elcano/Linked/LinkedVehicles-Winter-Spring2023/CAD/Trike assembly/cylinder.SLDPRT

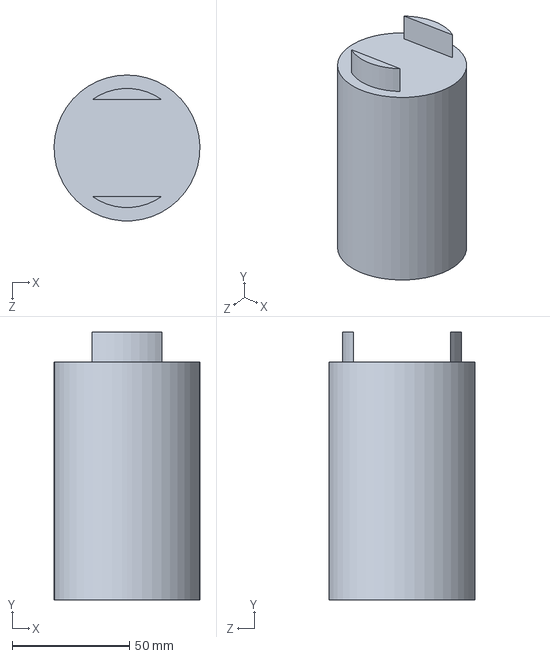
[picture p67: CAD file, 2023-06-08]
LinkedVehicles-Winter-Spring2023/CAD/Trike assembly/cylinder.SLDPRT
62.2 x 114.3 x 62.2 mm
