elcano/Linked/3_wire_connector_top.SLDPRT

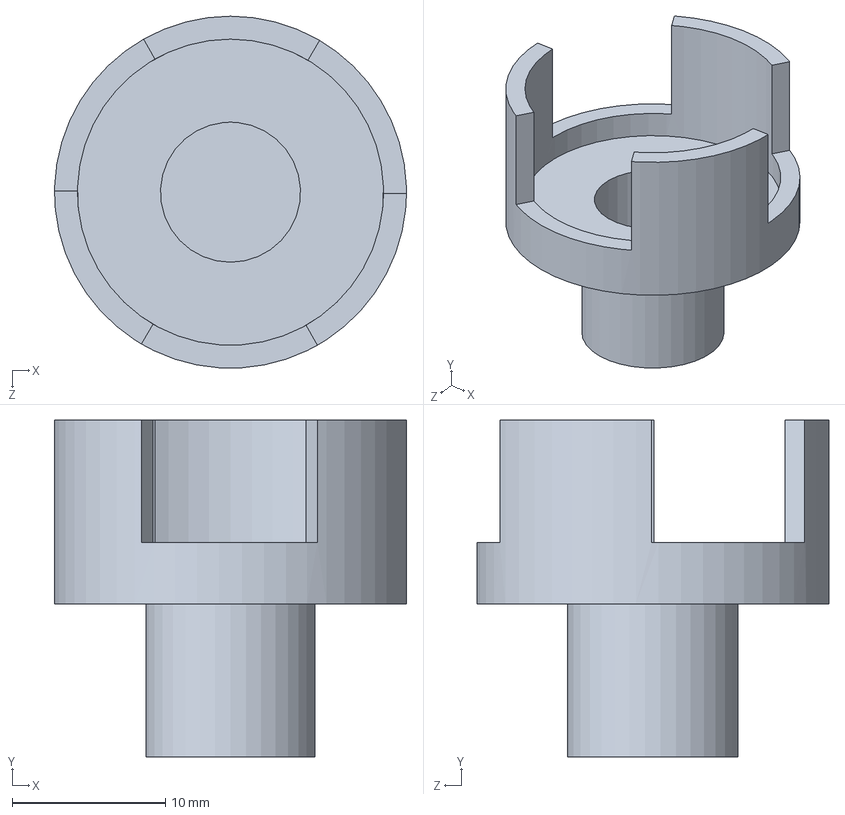
[picture p68: CAD file, 2023-06-08]
3_wire_connector_top.SLDPRT
23.0 x 22.0 x 23.0 mm
