elcano/Linked/LinkedVehicles-Winter-Spring2023/CAD/male and female- v2/UJoint.SLDPRT

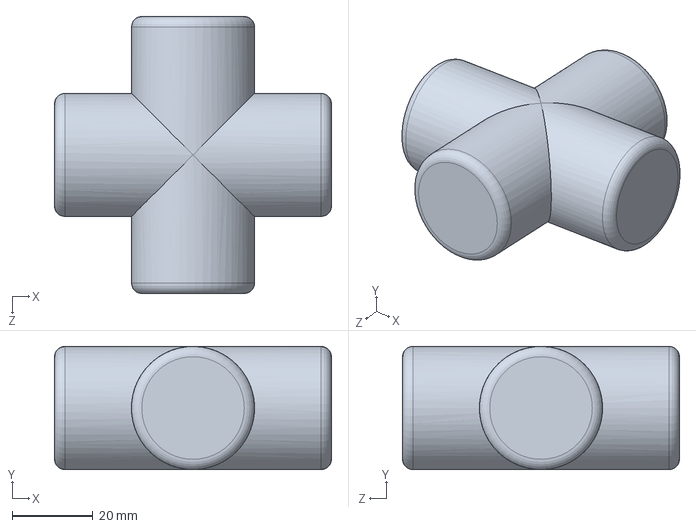
[picture p69: CAD file, 2023-06-08]
LinkedVehicles-Winter-Spring2023/CAD/male and female- v2/UJoint.SLDPRT
68.6 x 30.5 x 68.6 mm
