elcano/Linked/LinkedVehicles-Winter-Spring2023/CAD/male and female/Yoke2.SLDPRT

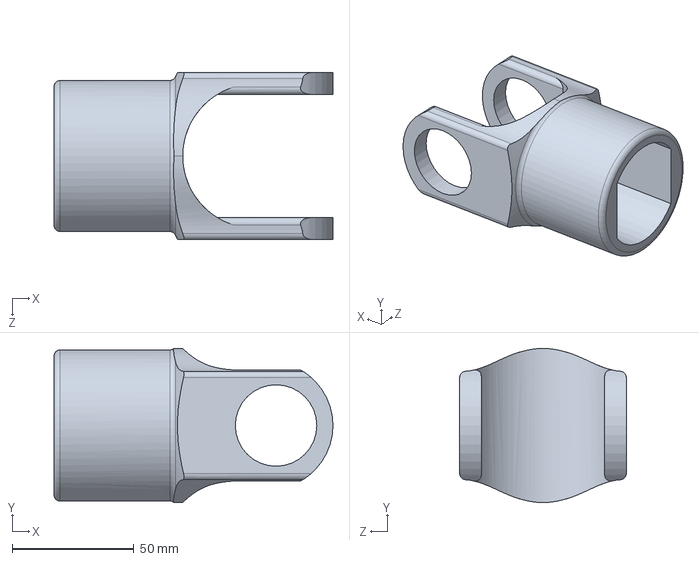
[picture p70: CAD file, 2023-06-08]
LinkedVehicles-Winter-Spring2023/CAD/male and female/Yoke2.SLDPRT
114.8 x 63.5 x 68.6 mm
