elcano/Linked/LinkedVehicles-Winter-Spring2023/CAD/Proto Lock 1.0/Rail_tapped hole.SLDPRT

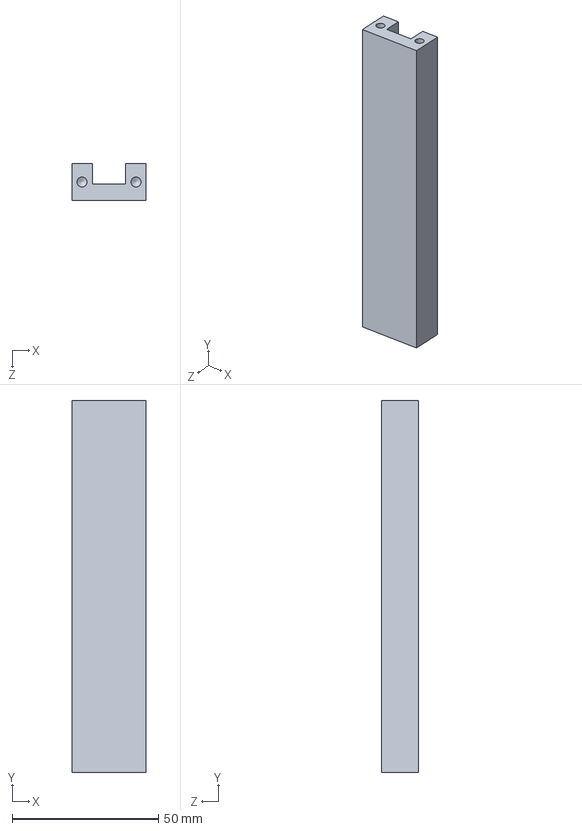
[picture p71: CAD file, 2023-06-08]
LinkedVehicles-Winter-Spring2023/CAD/Proto Lock 1.0/Rail_tapped hole.SLDPRT
25.4 x 127.0 x 12.7 mm
