elcano/Linked/LinkedVehicles-Winter-Spring2023/CAD/Proto Lock 2.0/Spool.SLDPRT

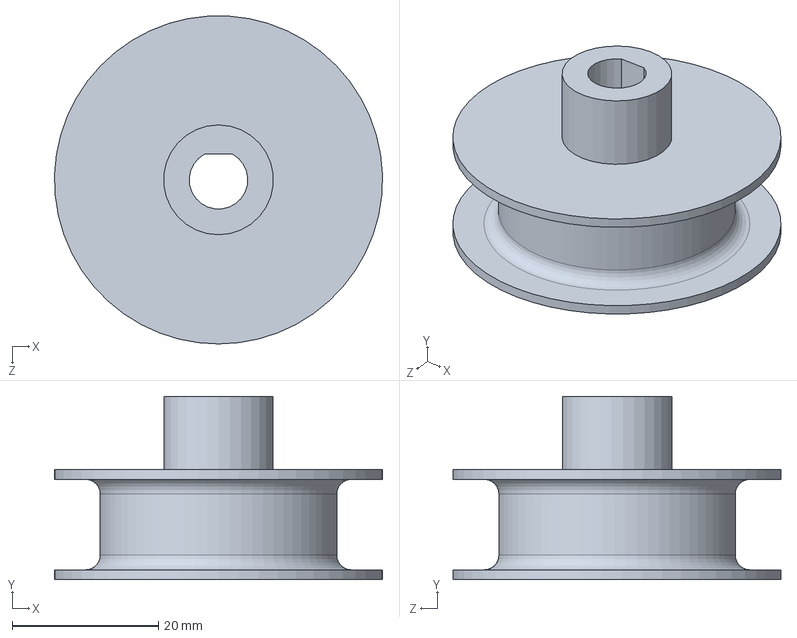
[picture p72: CAD file, 2023-06-08]
LinkedVehicles-Winter-Spring2023/CAD/Proto Lock 2.0/Spool.SLDPRT
44.8 x 25.0 x 44.8 mm
