elcano/Linked/LinkedVehicles-Winter-Spring2023/CAD/Trike assembly/Back mount plate.SLDPRT

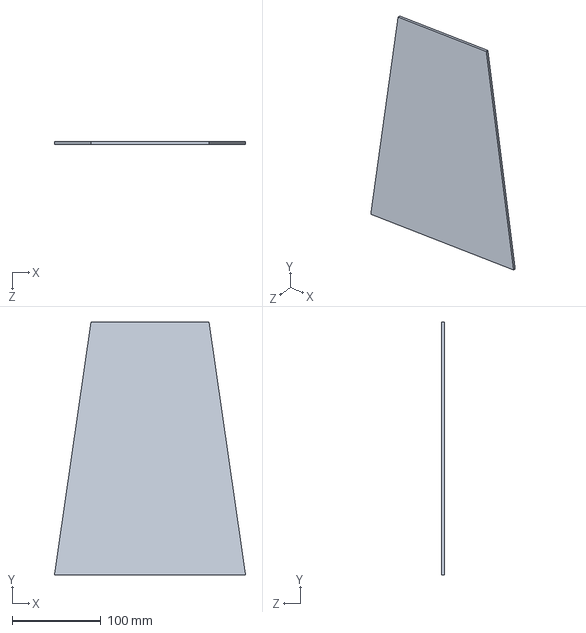
[picture p73: CAD file, 2023-06-08]
LinkedVehicles-Winter-Spring2023/CAD/Trike assembly/Back mount plate.SLDPRT
215.9 x 285.8 x 3.26 mm
