elcano/Linked/Cable_mangment_28mm.SLDPRT

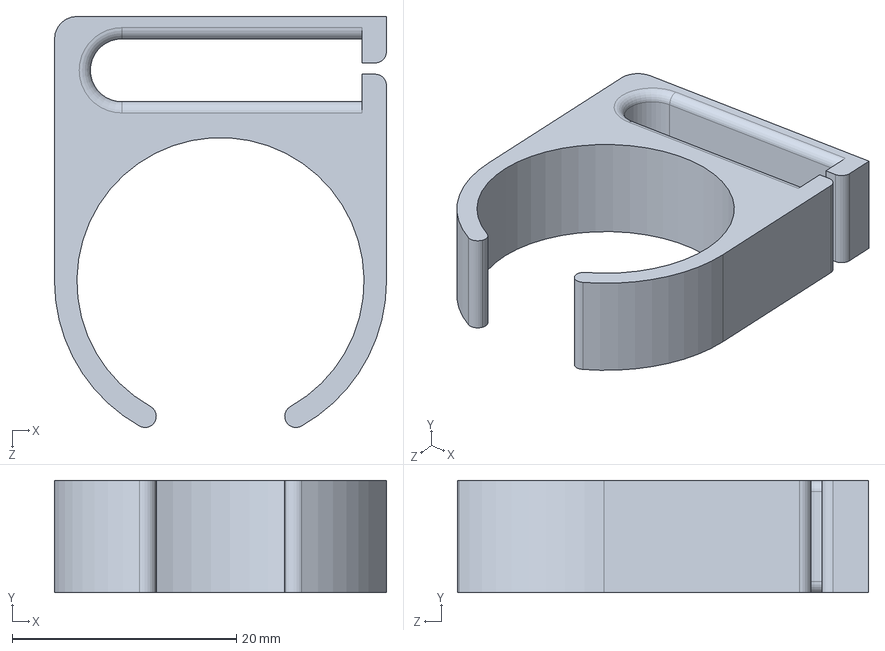
[picture p74: CAD file, 2023-06-08]
Cable_mangment_28mm.SLDPRT
29.6 x 10.0 x 36.7 mm
