elcano/Linked/LinkedVehicles-Winter-Spring2023/CAD/male and female- v2/lever lock.SLDPRT

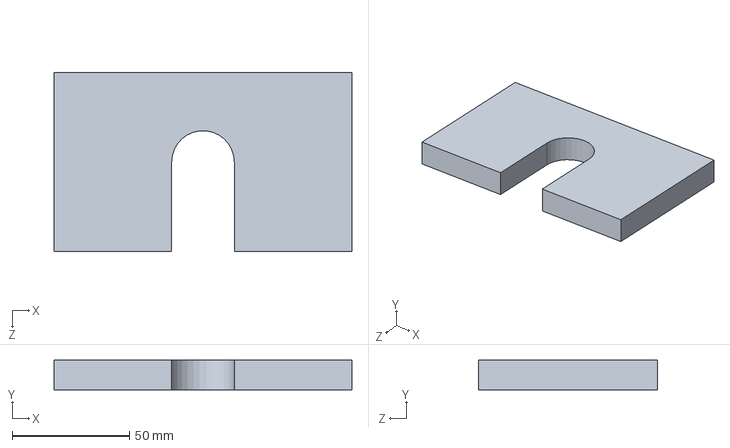
[picture p75: CAD file, 2023-06-08]
LinkedVehicles-Winter-Spring2023/CAD/male and female- v2/lever lock.SLDPRT
127.0 x 12.7 x 76.2 mm
