elcano/Linked/LinkedVehicles-Winter-Spring2023/CAD/New Female Part/Female Coupler Stock Materials.SLDPRT

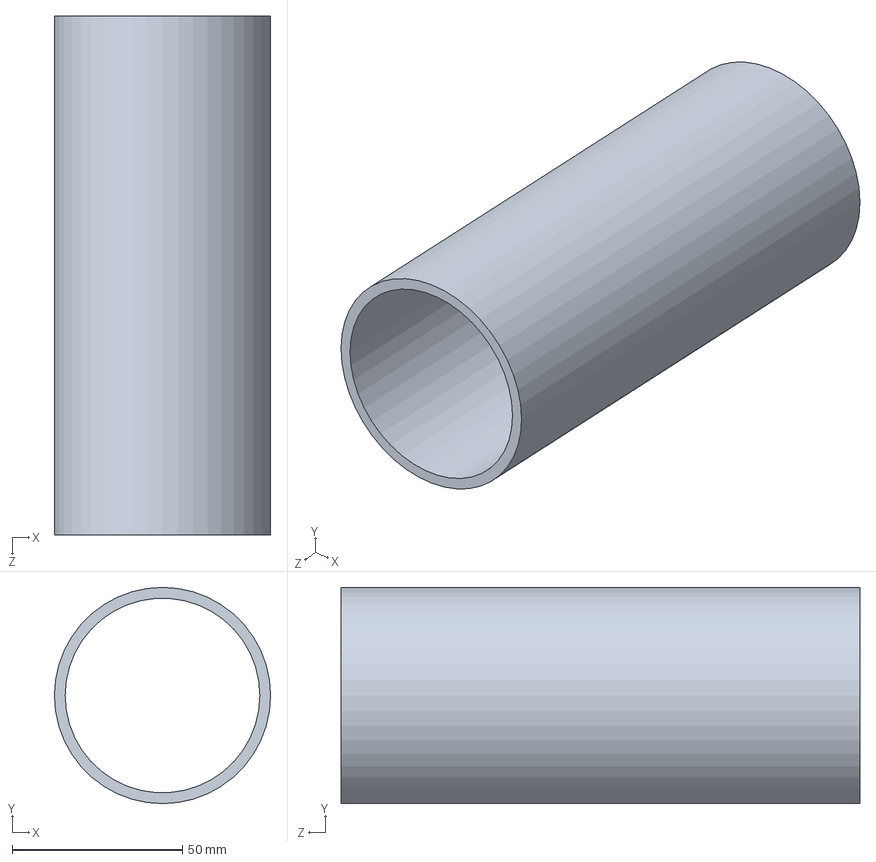
[picture p76: CAD file, 2023-06-08]
LinkedVehicles-Winter-Spring2023/CAD/New Female Part/Female Coupler Stock Materials.SLDPRT
63.5 x 63.5 x 152.4 mm
