elcano/Linked/LinkedVehicles-Winter-Spring2023/CAD/Proto Lock 2.0/Stepper.SLDPRT

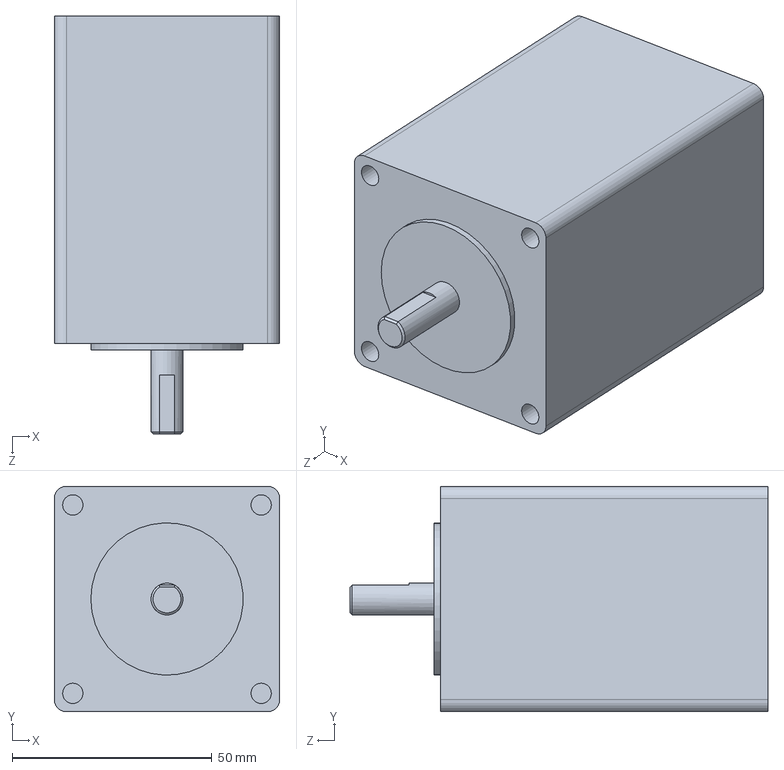
[picture p77: CAD file, 2023-06-08]
LinkedVehicles-Winter-Spring2023/CAD/Proto Lock 2.0/Stepper.SLDPRT
56.4 x 56.4 x 104.6 mm
