elcano/Linked/51_mm_tube_cable_mount.SLDPRT

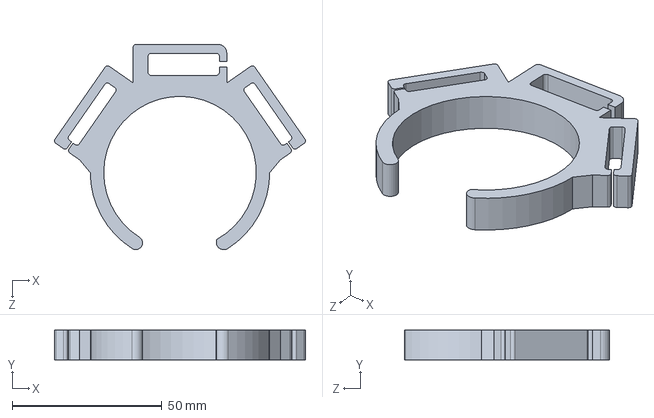
[picture p78: CAD file, 2023-06-08]
51_mm_tube_cable_mount.SLDPRT
83.9 x 10.0 x 68.7 mm
