elcano/Linked/LinkedVehicles-Winter-Spring2023/CAD/Trike assembly/Front mounting frame.SLDPRT

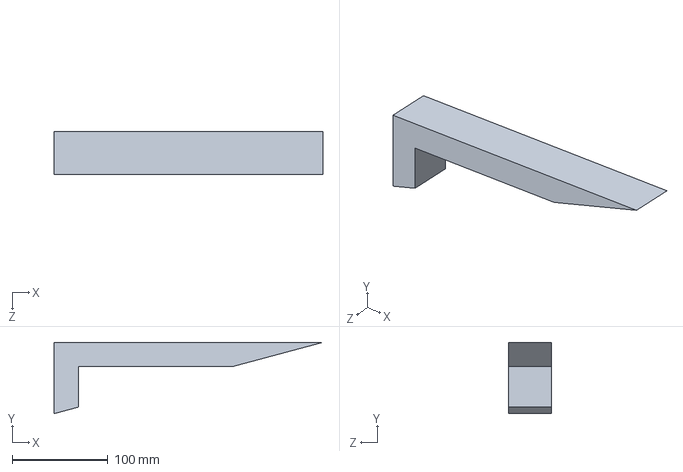
[picture p79: CAD file, 2023-06-08]
LinkedVehicles-Winter-Spring2023/CAD/Trike assembly/Front mounting frame.SLDPRT
280.4 x 74.3 x 45.0 mm
