elcano/Linked/LinkedVehicles-Winter-Spring2023/CAD/Proto Lock 1.0/CROSS.SLDPRT

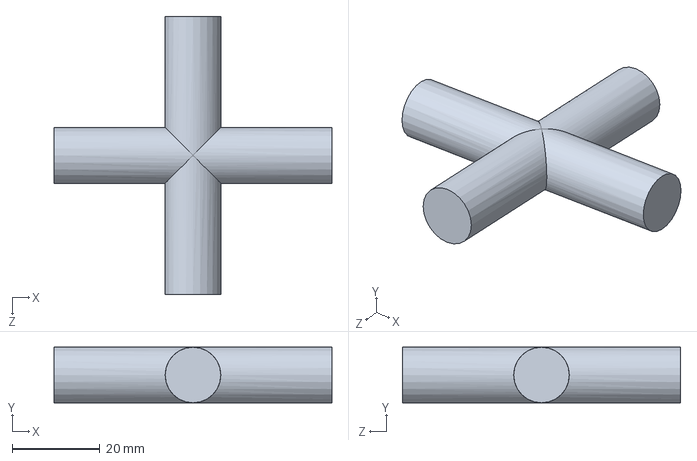
[picture p80: CAD file, 2023-06-08]
LinkedVehicles-Winter-Spring2023/CAD/Proto Lock 1.0/CROSS.SLDPRT
63.5 x 12.7 x 63.5 mm
