elcano/Linked/LinkedVehicles-Winter-Spring2023/CAD/Proto Lock 2.0/Pulley system pulley.SLDPRT

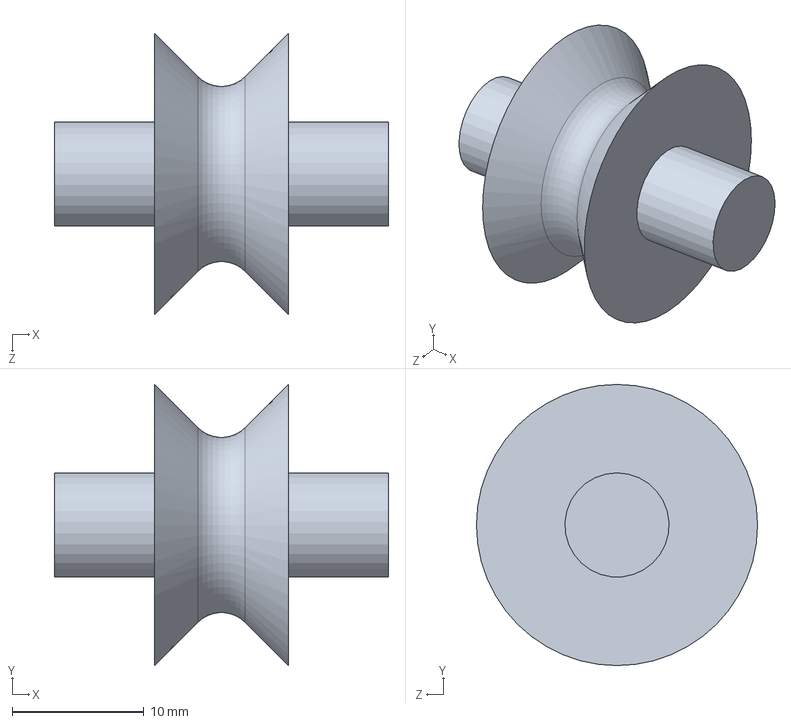
[picture p81: CAD file, 2023-06-08]
LinkedVehicles-Winter-Spring2023/CAD/Proto Lock 2.0/Pulley system pulley.SLDPRT
25.4 x 21.4 x 21.4 mm
