elcano/Linked/LinkedVehicles-Winter-Spring2023/CAD/Proto Lock 1.0/Lever lock.SLDPRT

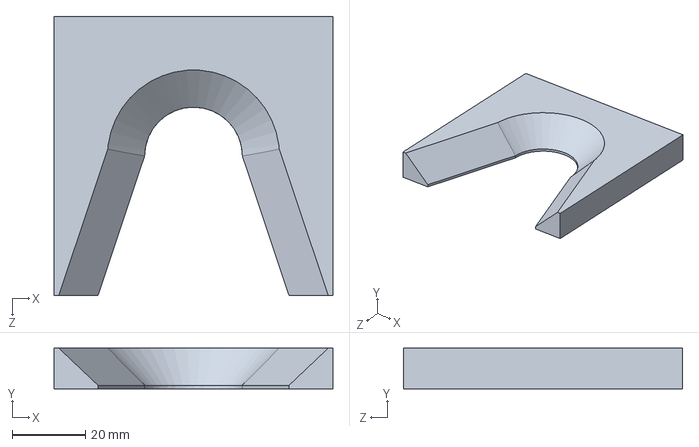
[picture p82: CAD file, 2023-06-08]
LinkedVehicles-Winter-Spring2023/CAD/Proto Lock 1.0/Lever lock.SLDPRT
76.2 x 11.1 x 76.2 mm
