elcano/Linked/LinkedVehicles-Winter-Spring2023/CAD/Proto Lock 2.0/Temp Bumper.SLDPRT

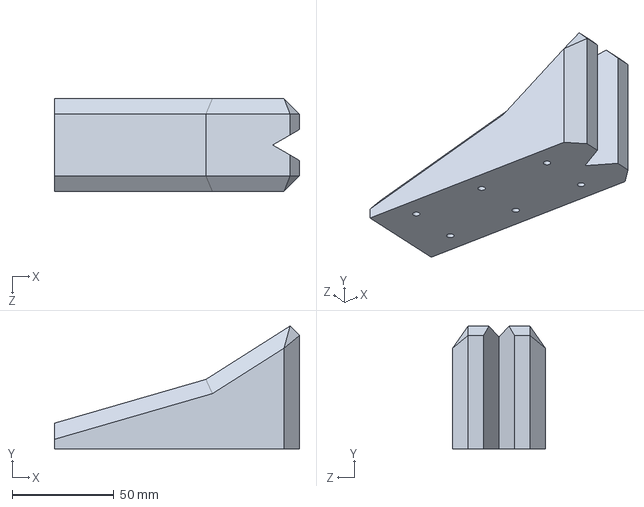
[picture p83: CAD file, 2023-06-08]
LinkedVehicles-Winter-Spring2023/CAD/Proto Lock 2.0/Temp Bumper.SLDPRT
120.7 x 60.5 x 45.7 mm
