elcano/Linked/LinkedVehicles-Winter-Spring2023/CAD/Trike assembly/Male Shaft (2).SLDPRT

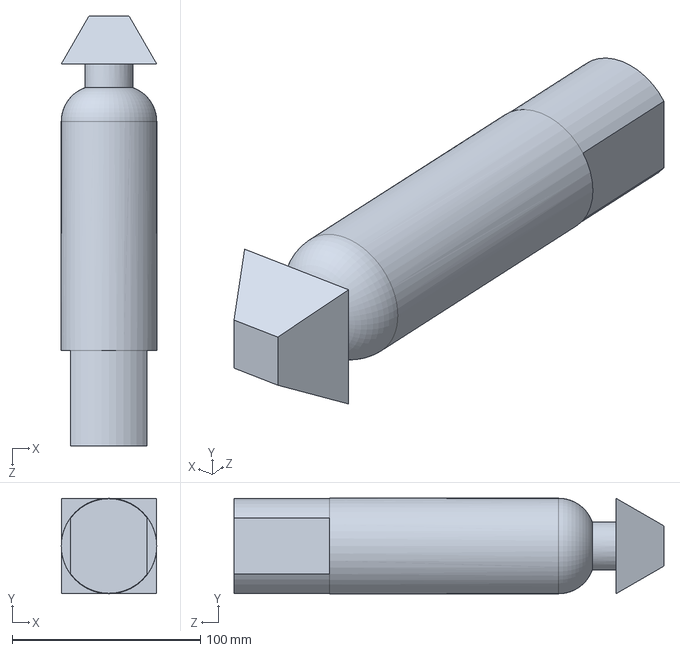
[picture p84: CAD file, 2023-06-08]
LinkedVehicles-Winter-Spring2023/CAD/Trike assembly/Male Shaft (2).SLDPRT
50.8 x 50.8 x 228.6 mm
