elcano/Linked/LinkedVehicles-Winter-Spring2023/CAD/male and female/lever lock.SLDPRT

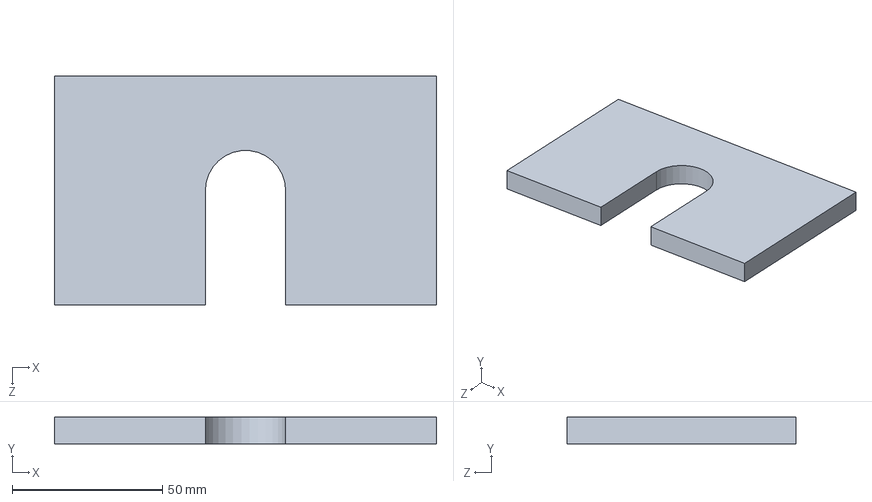
[picture p85: CAD file, 2023-06-08]
LinkedVehicles-Winter-Spring2023/CAD/male and female/lever lock.SLDPRT
127.0 x 8.89 x 76.2 mm
