elcano/Linked/LinkedVehicles-Winter-Spring2023/CAD/Proto Lock 1.0/1x.5 barstock.SLDPRT

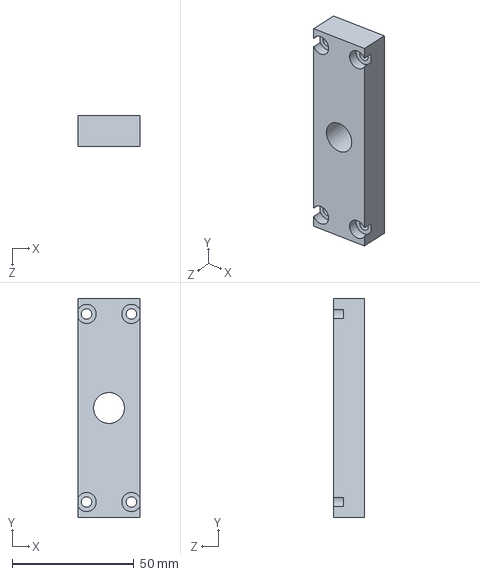
[picture p86: CAD file, 2023-06-08]
LinkedVehicles-Winter-Spring2023/CAD/Proto Lock 1.0/1x.5 barstock.SLDPRT
25.4 x 90.0 x 12.7 mm
