elcano/Linked/LinkedVehicles-Winter-Spring2023/CAD/Proto Lock 2.0/Baseplate V2.SLDPRT

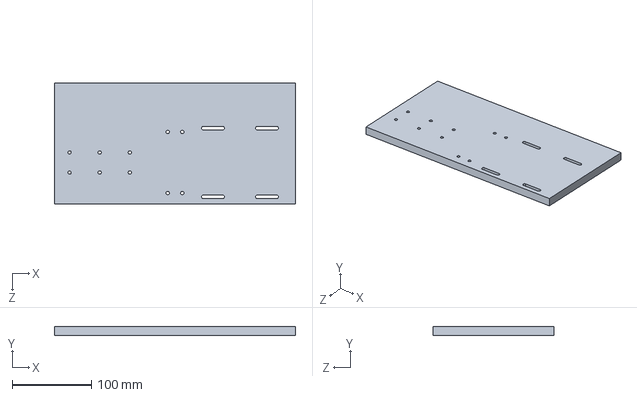
[picture p87: CAD file, 2023-06-08]
LinkedVehicles-Winter-Spring2023/CAD/Proto Lock 2.0/Baseplate V2.SLDPRT
304.8 x 11.1 x 152.4 mm
