elcano/Linked/LinkedVehicles-Winter-Spring2023/CAD/Proto Lock 1.0/ARMS.SLDPRT

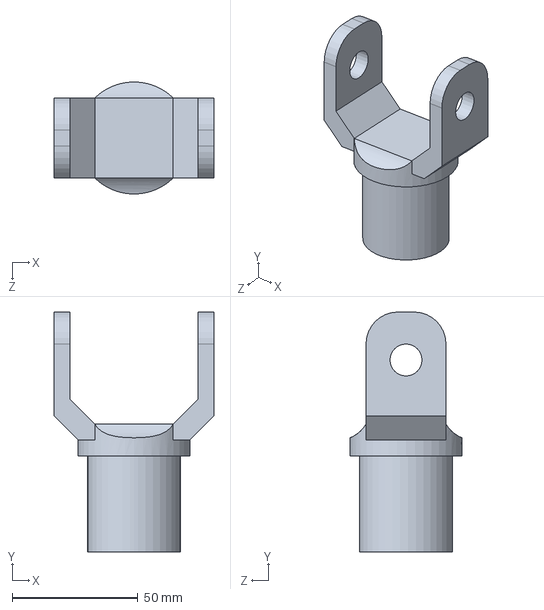
[picture p88: CAD file, 2023-06-08]
LinkedVehicles-Winter-Spring2023/CAD/Proto Lock 1.0/ARMS.SLDPRT
63.5 x 95.2 x 44.5 mm
