elcano/Linked/LinkedVehicles-Winter-Spring2023/CAD/Proto Lock 2.0/ARMS.SLDPRT

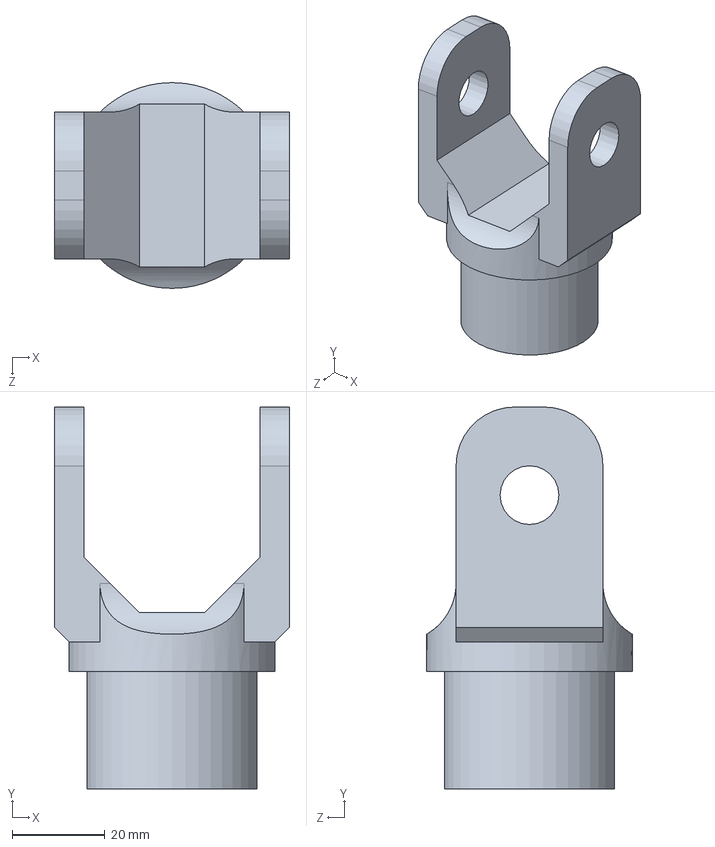
[picture p89: CAD file, 2023-06-08]
LinkedVehicles-Winter-Spring2023/CAD/Proto Lock 2.0/ARMS.SLDPRT
50.8 x 82.5 x 44.5 mm
