elcano/Linked/LinkedVehicles-Winter-Spring2023/CAD/Proto Lock 2.0/Spool small.SLDPRT

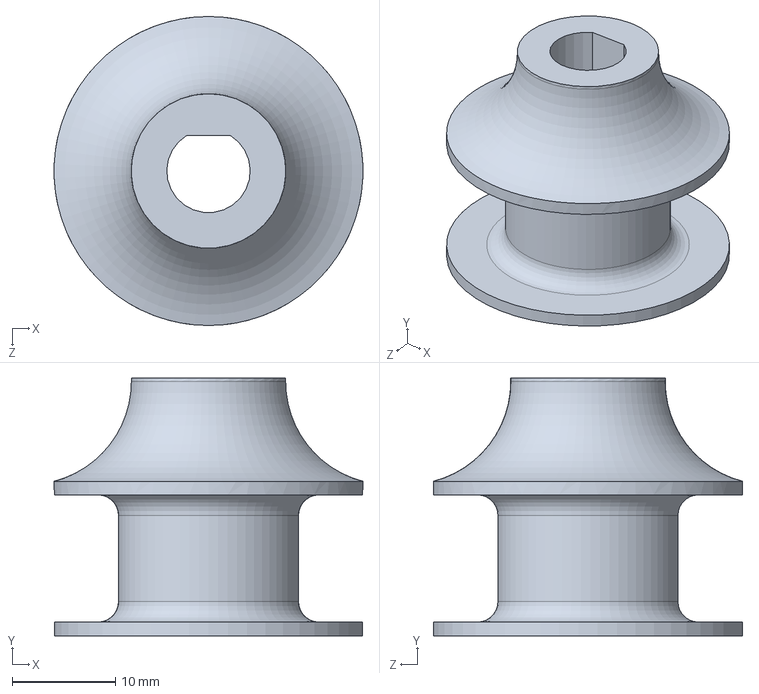
[picture p90: CAD file, 2023-06-08]
LinkedVehicles-Winter-Spring2023/CAD/Proto Lock 2.0/Spool small.SLDPRT
30.0 x 25.0 x 30.0 mm
