elcano/Linked/LinkedVehicles-Winter-Spring2023/CAD/Trike assembly/Front mounting holder.SLDPRT

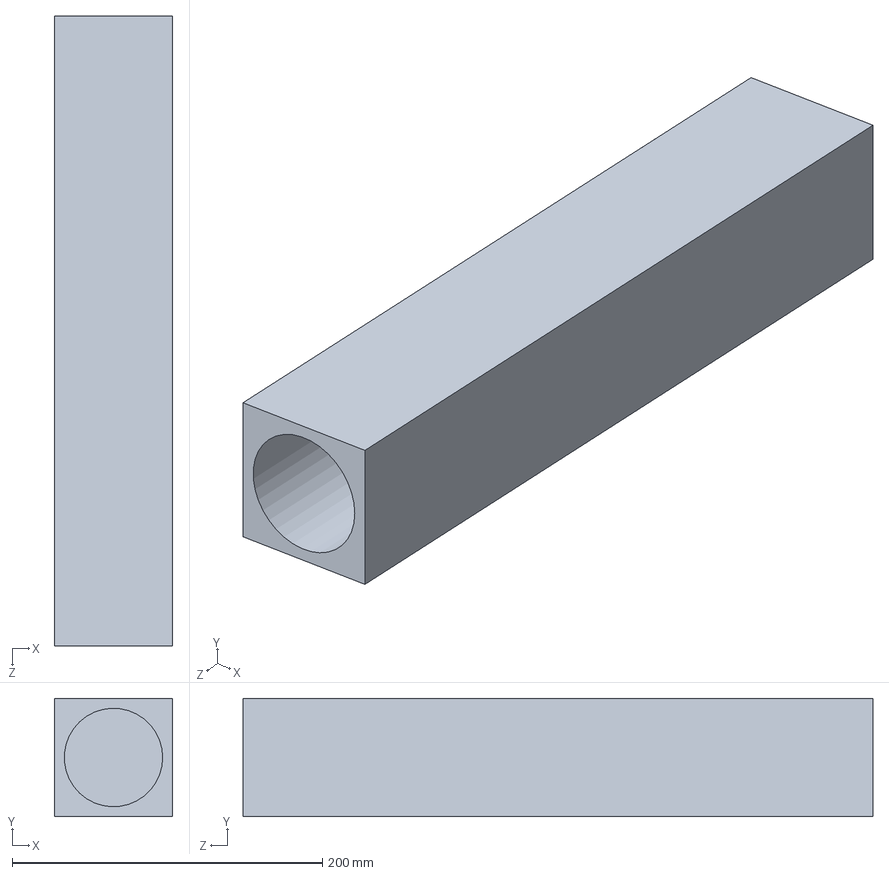
[picture p91: CAD file, 2023-06-08]
LinkedVehicles-Winter-Spring2023/CAD/Trike assembly/Front mounting holder.SLDPRT
76.2 x 76.2 x 406.4 mm
