elcano/Linked/LinkedVehicles-Winter-Spring2023/CAD/Proto Lock 1.0/Holding Bands.SLDPRT

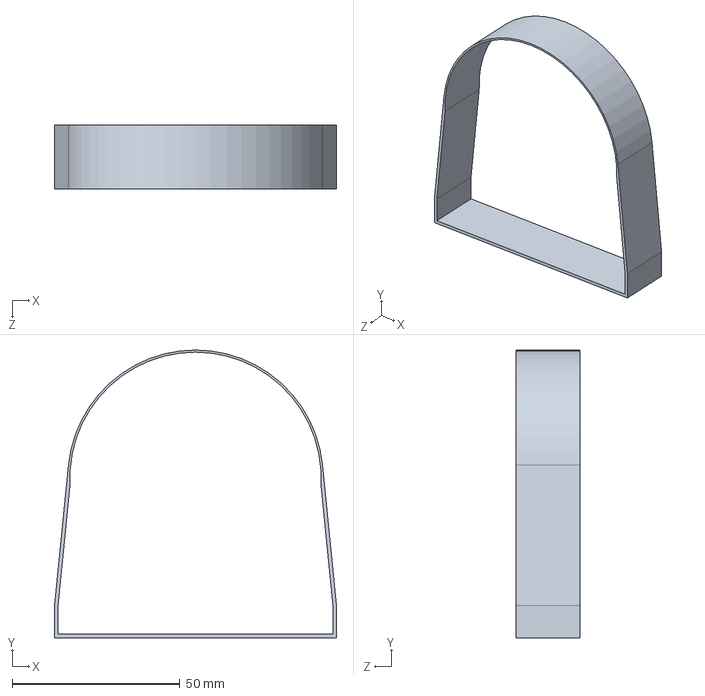
[picture p92: CAD file, 2023-06-08]
LinkedVehicles-Winter-Spring2023/CAD/Proto Lock 1.0/Holding Bands.SLDPRT
84.1 x 85.9 x 19.1 mm
