elcano/Linked/LinkedVehicles-Winter-Spring2023/CAD/Proto Lock 2.0/CROSS.SLDPRT

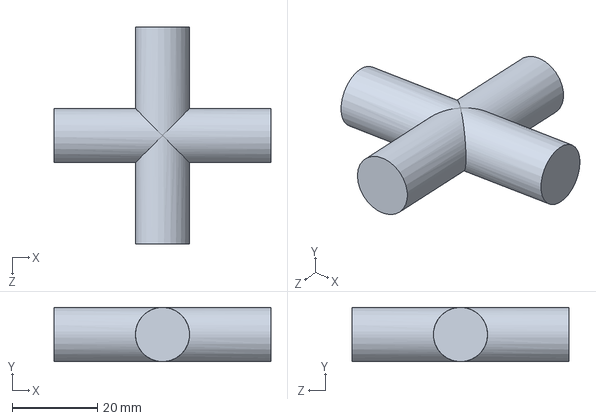
[picture p93: CAD file, 2023-06-08]
LinkedVehicles-Winter-Spring2023/CAD/Proto Lock 2.0/CROSS.SLDPRT
50.8 x 12.7 x 50.8 mm
