elcano/Linked/LinkedVehicles-Winter-Spring2023/CAD/Proto Lock 2.0/Pulley holder.SLDPRT

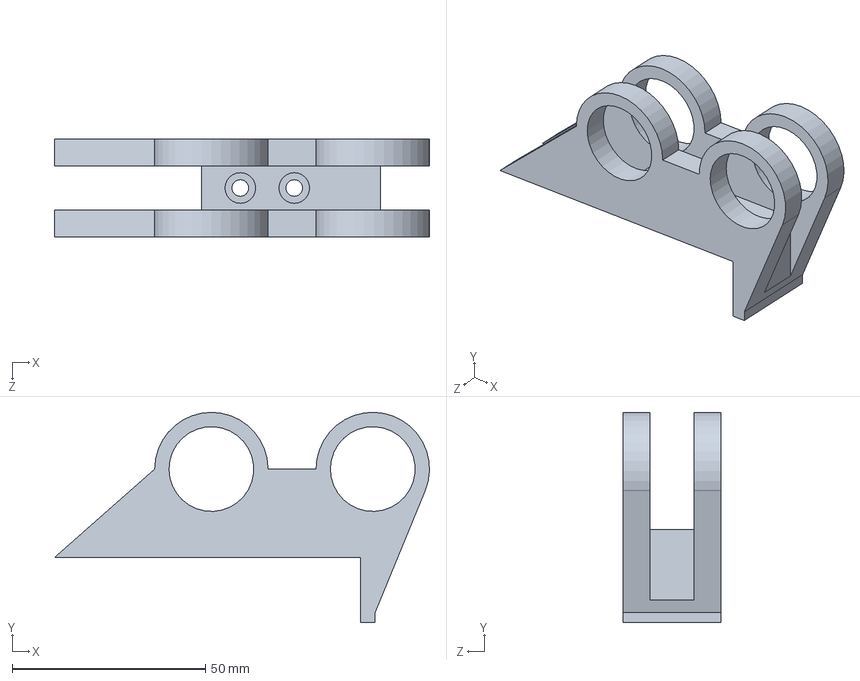
[picture p94: CAD file, 2023-06-08]
LinkedVehicles-Winter-Spring2023/CAD/Proto Lock 2.0/Pulley holder.SLDPRT
97.1 x 54.5 x 25.4 mm
