elcano/Linked/LinkedVehicles-Winter-Spring2023/CAD/Proto Lock 2.0/Stepper bracket.SLDPRT

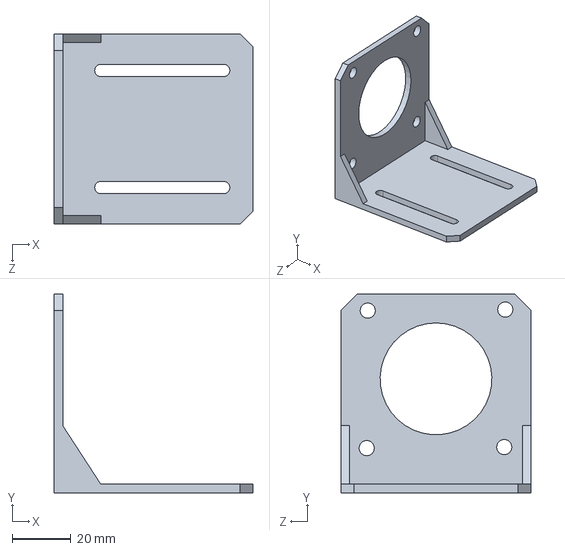
[picture p95: CAD file, 2023-06-08]
LinkedVehicles-Winter-Spring2023/CAD/Proto Lock 2.0/Stepper bracket.SLDPRT
68.0 x 68.0 x 65.0 mm
